AndreAdrian/65C02-ICP/65C02_MiniICP.kicad_sch

## KiCad design 65C02_MiniICP.kicad_sch (2022-08-23)

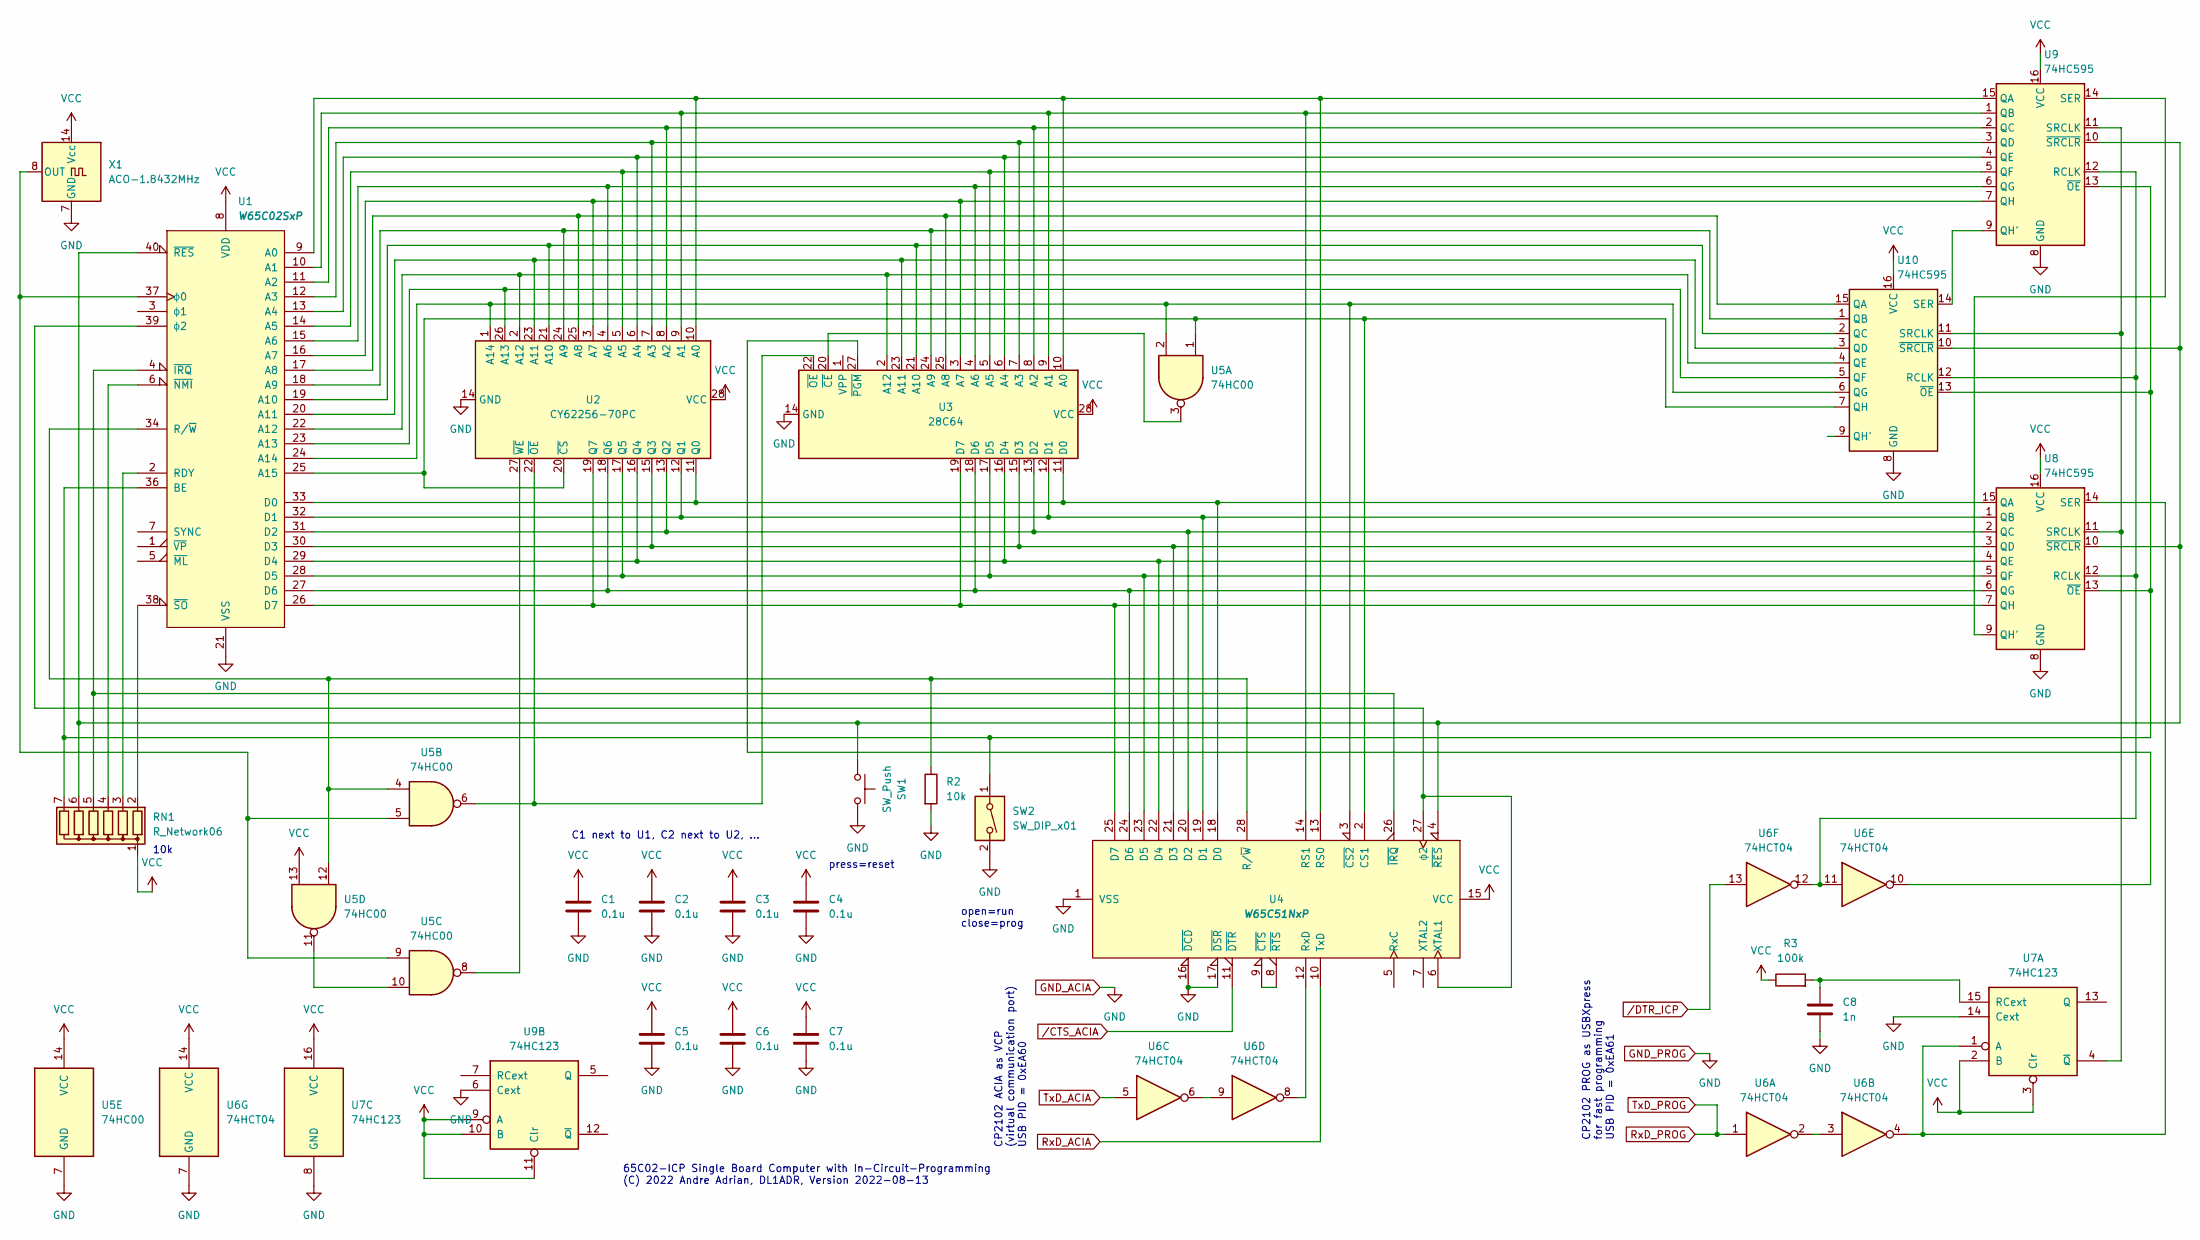
[picture p3: schematic 65C02_MiniICP.kicad_sch]

Parts:
C1, C2, C3, C4, C5, C6, C7: 0.1u
C8: 1n
R2: 10k
R3: 100k
RN1: R_Network06; R_Array_SIP7
SW1: SW_Push
SW2: SW_DIP_x01
U1: W65C02SxP
U2: CY62256-70PC; DIP-28_W15.24mm
U3: 28C64; DIP-28_W15.24mm
U4: W65C51NxP
U5: 74HC00
U6: 74HCT04
U7, U9: 74HC123
U8, U10: 74HC595
X1: ACO-1.8432MHz; Oscillator_DIP-14

Connections:
unnamed: C8.1, R3.2, U7.15 (RCext)
unnamed: R2.1, U1.34 (R/~W), U4.28 (R/~W), U5.4, U5.12
unnamed: RN1.2 (R1), U1.38 (~SO)
unnamed: RN1.3 (R2), U1.2 (RDY)
unnamed: RN1.4 (R3), U1.6 (~NMI)
unnamed: RN1.5 (R4), U1.4 (~IRQ), U4.26 (~IRQ)
unnamed: RN1.6 (R5), SW1.1, U1.40 (~RES), U4.4 (~RES), U8.10 (~SRCLR), U9.10 (~SRCLR), U10.10 (~SRCLR)
unnamed: RN1.7 (R6), SW2.1, U1.36 (BE), U8.13 (~OE), U9.13 (~OE), U10.13 (~OE)
unnamed: U1.9 (A0), U2.10 (A0), U3.10 (A0), U4.13 (RS0), U9.15 (QA)
unnamed: U1.10 (A1), U2.9 (A1), U3.9 (A1), U4.14 (RS1), U9.1 (QB)
unnamed: U1.11 (A2), U2.8 (A2), U3.8 (A2), U9.2 (QC)
unnamed: U1.12 (A3), U2.7 (A3), U3.7 (A3), U9.3 (QD)
unnamed: U1.13 (A4), U2.6 (A4), U3.6 (A4), U9.4 (QE)
unnamed: U1.14 (A5), U2.5 (A5), U3.5 (A5), U9.5 (QF)
unnamed: U1.15 (A6), U2.4 (A6), U3.4 (A6), U9.6 (QG)
unnamed: U1.16 (A7), U2.3 (A7), U3.3 (A7), U9.7 (QH)
unnamed: U1.17 (A8), U2.25 (A8), U3.25 (A8), U10.15 (QA)
unnamed: U1.18 (A9), U2.24 (A9), U3.24 (A9), U10.1 (QB)
unnamed: U1.19 (A10), U2.21 (A10), U3.21 (A10), U10.2 (QC)
unnamed: U1.20 (A11), U2.23 (A11), U3.23 (A11), U10.3 (QD)
unnamed: U1.22 (A12), U2.2 (A12), U3.2 (A12), U10.4 (QE)
unnamed: U1.23 (A13), U2.26 (A13), U10.5 (QF)
unnamed: U1.24 (A14), U2.1 (A14), U4.3 (~CS2), U5.2, U10.6 (QG)
unnamed: U1.25 (A15), U2.20 (~CS), U4.2 (CS1), U5.1, U10.7 (QH)
unnamed: U1.26 (D7), U2.19 (Q7), U3.19 (D7), U4.25 (D7), U8.7 (QH)
unnamed: U1.27 (D6), U2.18 (Q6), U3.18 (D6), U4.24 (D6), U8.6 (QG)
unnamed: U1.28 (D5), U2.17 (Q5), U3.17 (D5), U4.23 (D5), U8.5 (QF)
unnamed: U1.29 (D4), U2.16 (Q4), U3.16 (D4), U4.22 (D4), U8.4 (QE)
unnamed: U1.30 (D3), U2.15 (Q3), U3.15 (D3), U4.21 (D3), U8.3 (QD)
unnamed: U1.31 (D2), U2.13 (Q2), U3.13 (D2), U4.20 (D2), U8.2 (QC)
unnamed: U1.32 (D1), U2.12 (Q1), U3.12 (D1), U4.19 (D1), U8.1 (QB)
unnamed: U1.33 (D0), U2.11 (Q0), U3.11 (D0), U4.18 (D0), U8.15 (QA)
unnamed: U1.37 (ϕ0), U5.5, U5.9, X1.8 (OUT)
unnamed: U1.39 (ϕ2), U4.6 (XTAL1), U4.27 (ϕ2)
unnamed: U2.22 (~OE), U3.22 (~OE), U5.6
unnamed: U2.27 (~WE), U5.8
unnamed: U3.20 (~CE), U5.3
unnamed: U3.27 (~PGM), U6.10
unnamed: U4.8 (~RTS), U4.9 (~CTS)
unnamed: U4.12 (RxD), U6.8
unnamed: U4.16 (~DCD), U4.17 (~DSR)
unnamed: U5.10, U5.11
unnamed: U6.2, U6.3
unnamed: U6.4, U7.1 (A), U8.14 (SER)
unnamed: U6.6, U6.9
unnamed: U7.2 (B), U7.3 (Clr)
unnamed: U8.9 (QH'), U9.14 (SER)
unnamed: U9.9 (QH'), U9.10 (~SRCLR), U9.11 (SRCLK)
unnamed: U7.4 (~Q), U8.11 (SRCLK), U9.11 (SRCLK), U10.11 (SRCLK)
unnamed: U6.11, U6.12, U8.12 (RCLK), U9.12 (RCLK), U10.12 (RCLK)
unnamed: U9.9 (QH'), U10.14 (SER)
RxD_ACIA: U4.10 (TxD)
RxD_PROG: U6.1
TxD_ACIA: U6.5
/CTS_ACIA: U4.11 (~DTR)
/DTR_ICP: U6.13

Notes on the sheet:
10k
CP2102 ACIA as VCP (virtual communication port) USB PID = 0xEA60
CP2102 PROG as USBXpress for fast programming USB PID = 0xEA61
open=run close=prog
C1 next to U1, C2 next to U2, ...
65C02-ICP Single Board Computer with In-Circuit-Programming (C) 2022 Andre Adrian, DL1ADR, Version 2022-08-13
press=reset
